karomancer/uddermayhem/BovineBaristaGame/Assets/Sprites/background@2x.png

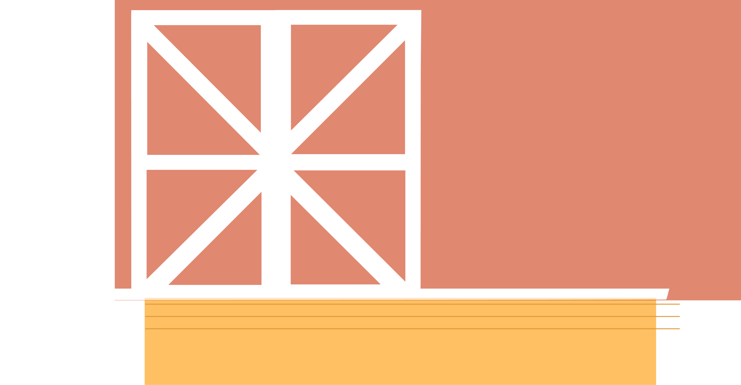
BovineBaristaGame/Assets/Sprites/background@2x.png
