karomancer/uddermayhem/BovineBaristaGame/Assets/Sprites/counter@2x.png

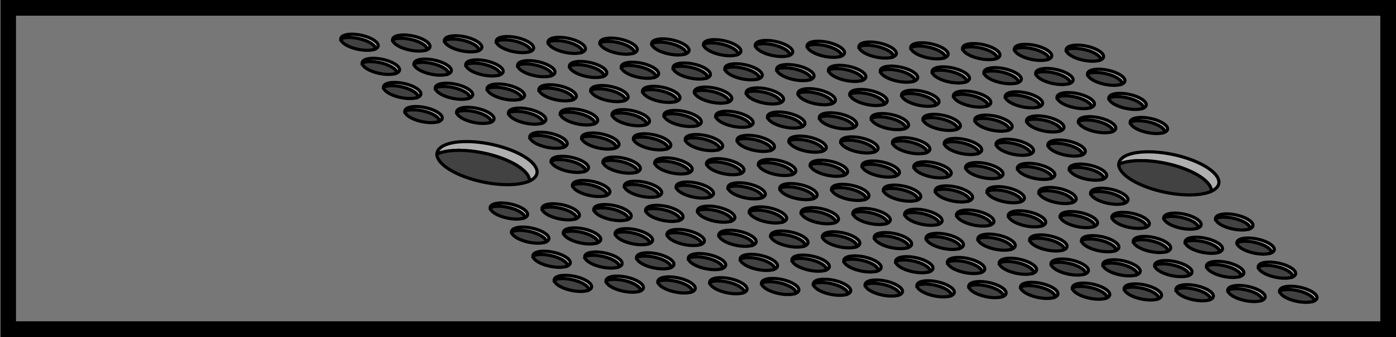
BovineBaristaGame/Assets/Sprites/counter@2x.png
