karomancer/uddermayhem/BovineBaristaGame/Assets/Sprites/cowBase@2x.png

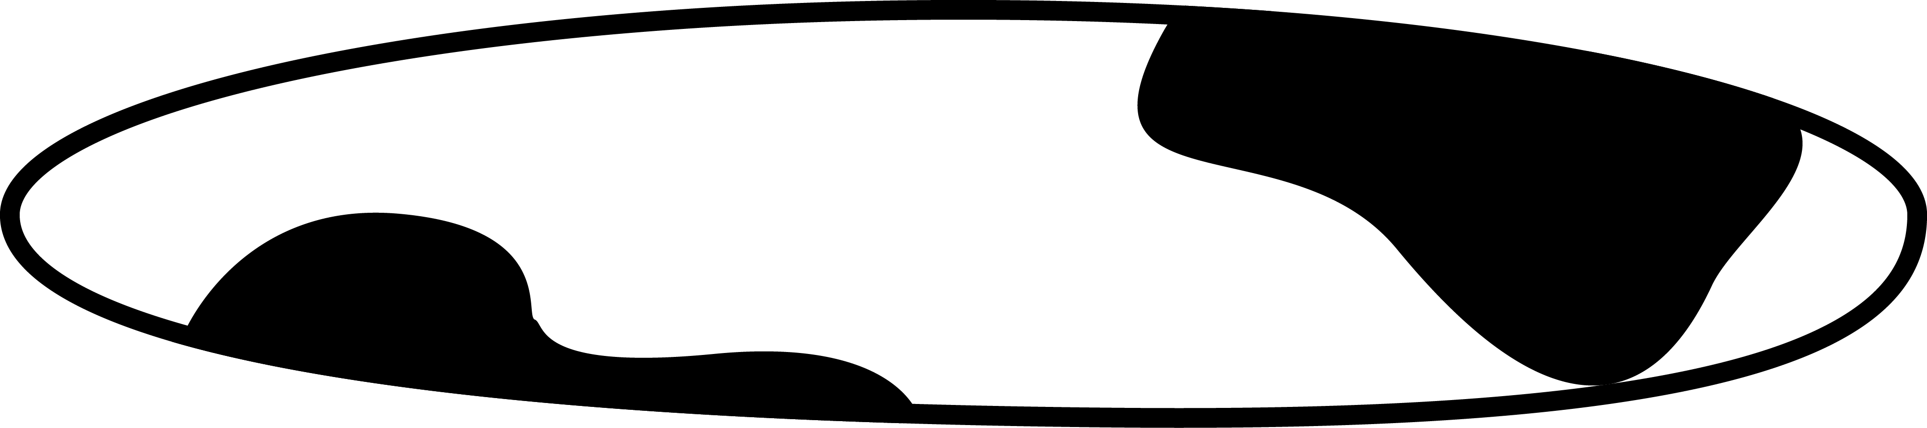
BovineBaristaGame/Assets/Sprites/cowBase@2x.png
