karomancer/uddermayhem/BovineBaristaGame/Assets/Sprites/lady_spritemap@2x-8.png

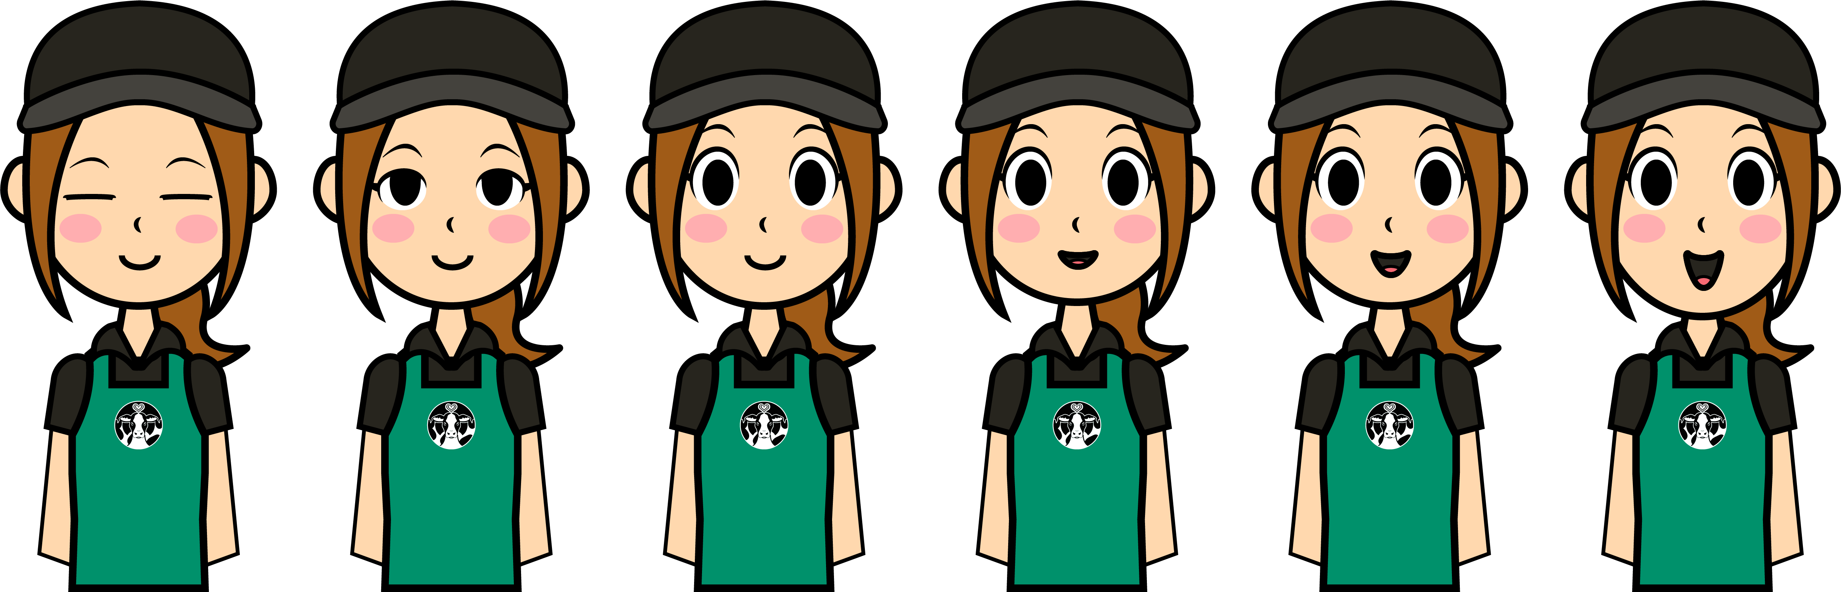
BovineBaristaGame/Assets/Sprites/lady_spritemap@2x-8.png
