karomancer/uddermayhem/BovineBaristaGame/Assets/Sprites/MoosicCoffee@2x.png

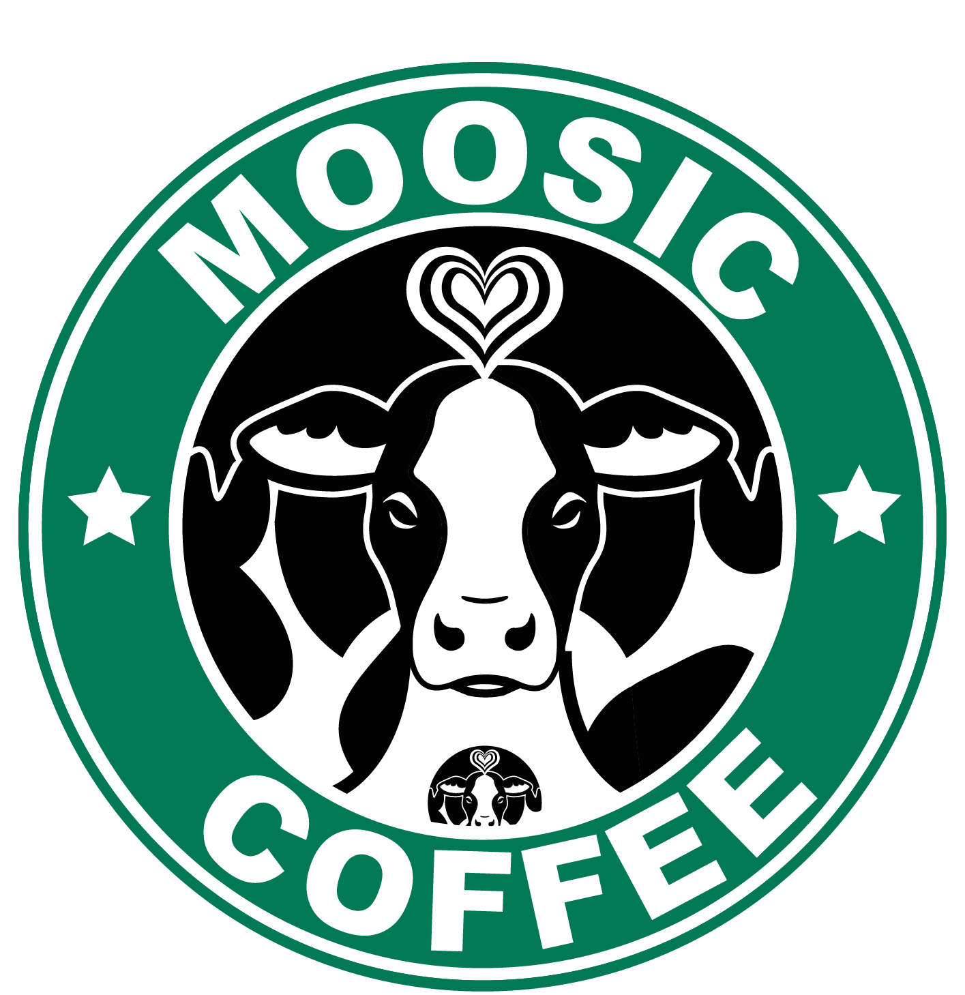
BovineBaristaGame/Assets/Sprites/MoosicCoffee@2x.png
