karomancer/uddermayhem/BovineBaristaGame/Assets/Sprites/MoosicCoffeeCup@2x.png

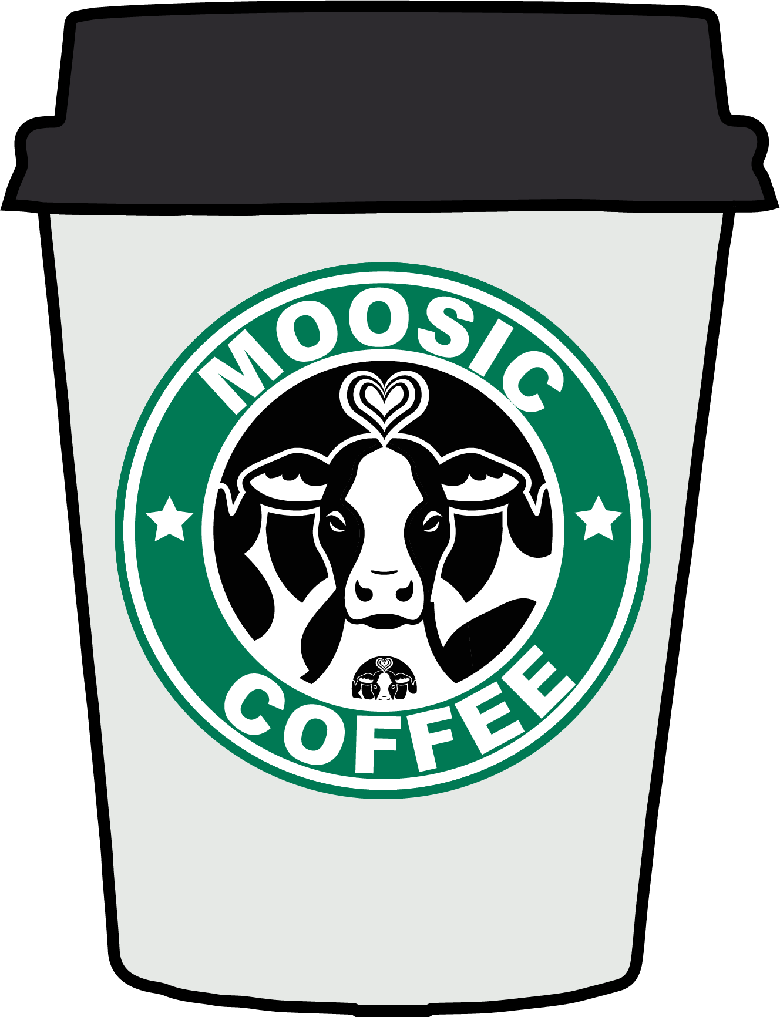
BovineBaristaGame/Assets/Sprites/MoosicCoffeeCup@2x.png
