karomancer/uddermayhem/BovineBaristaGame/Assets/Sprites/teatSpritesheet@2x 1.png

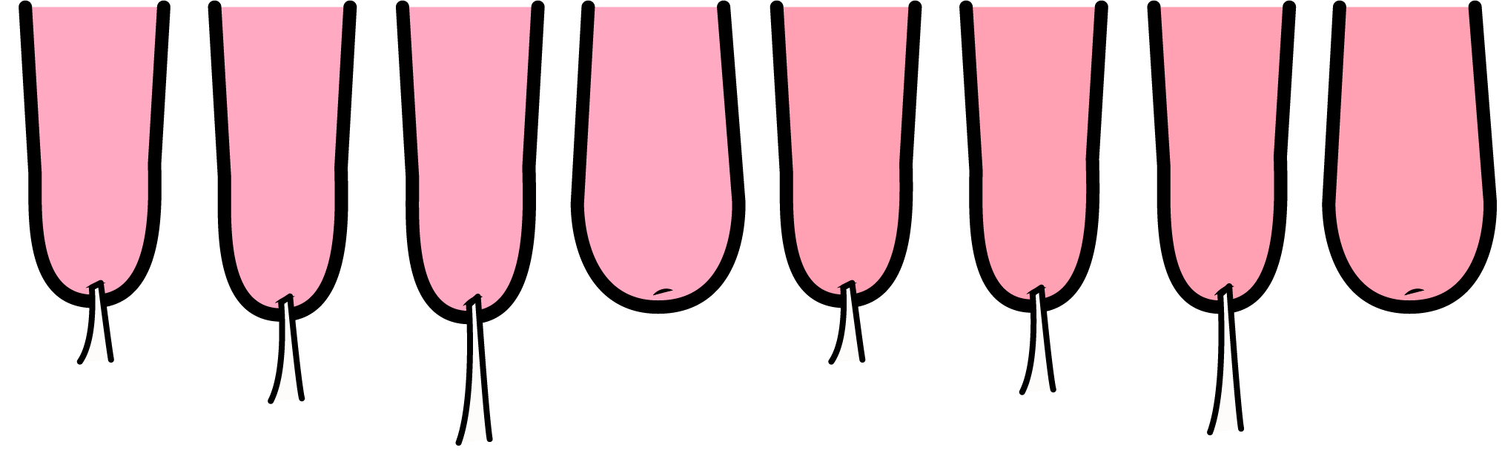
BovineBaristaGame/Assets/Sprites/teatSpritesheet@2x 1.png
