karomancer/uddermayhem/BovineBaristaGame/Assets/Sprites/TitleScreen/2x/Cloud@2x-8.png

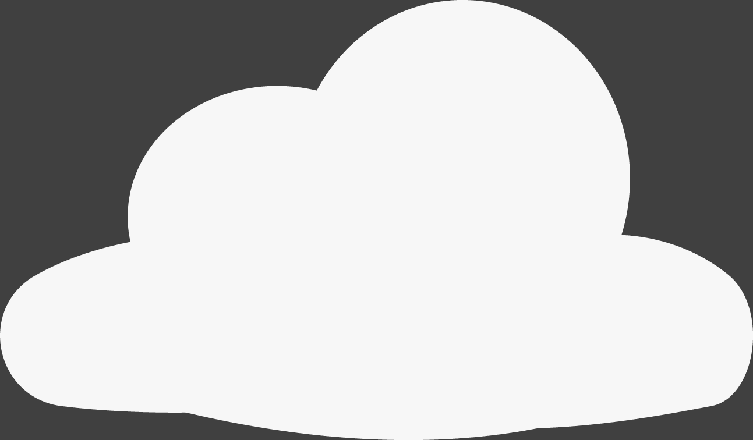
BovineBaristaGame/Assets/Sprites/TitleScreen/2x/Cloud@2x-8.png
