karomancer/uddermayhem/BovineBaristaGame/Assets/Sprites/TitleScreen/2x/MoosicCafe@2x-8.png

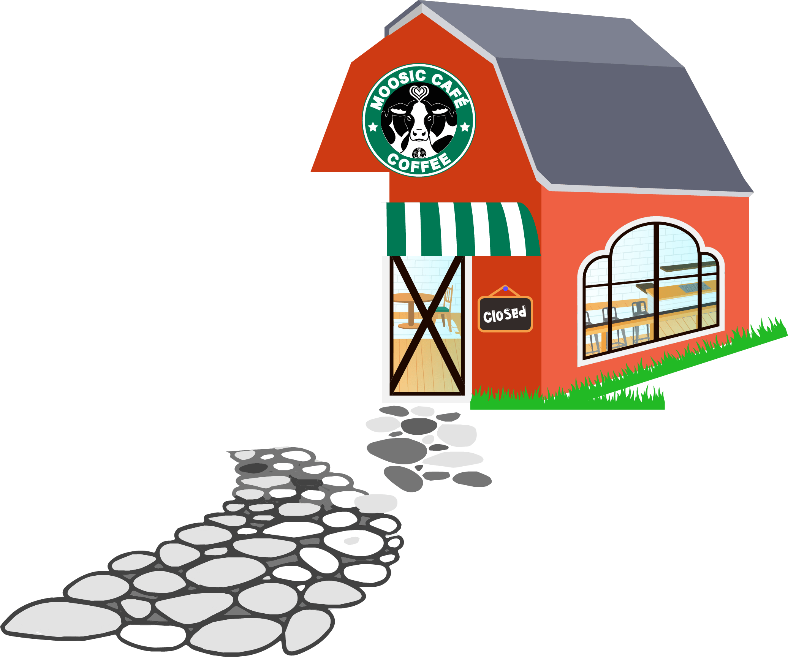
BovineBaristaGame/Assets/Sprites/TitleScreen/2x/MoosicCafe@2x-8.png
