karomancer/uddermayhem/BovineBaristaGame/Assets/Sprites/TitleScreen/2x/Sun@2x-8.png

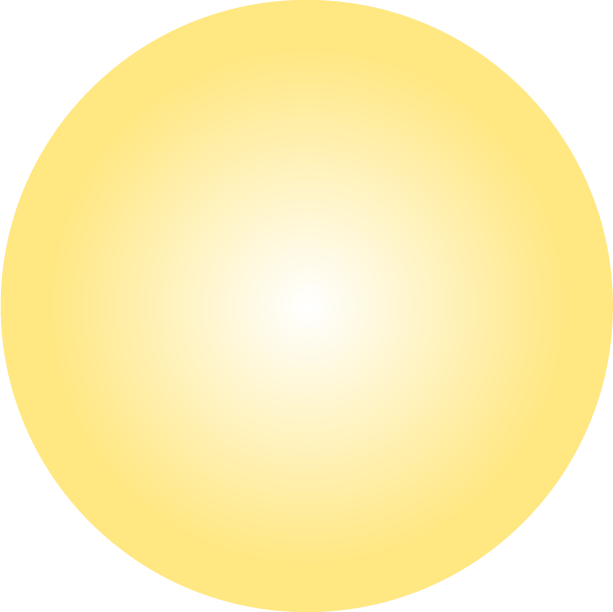
BovineBaristaGame/Assets/Sprites/TitleScreen/2x/Sun@2x-8.png
