karomancer/uddermayhem/BovineBaristaGame/Assets/squeezeMessage@2x.png

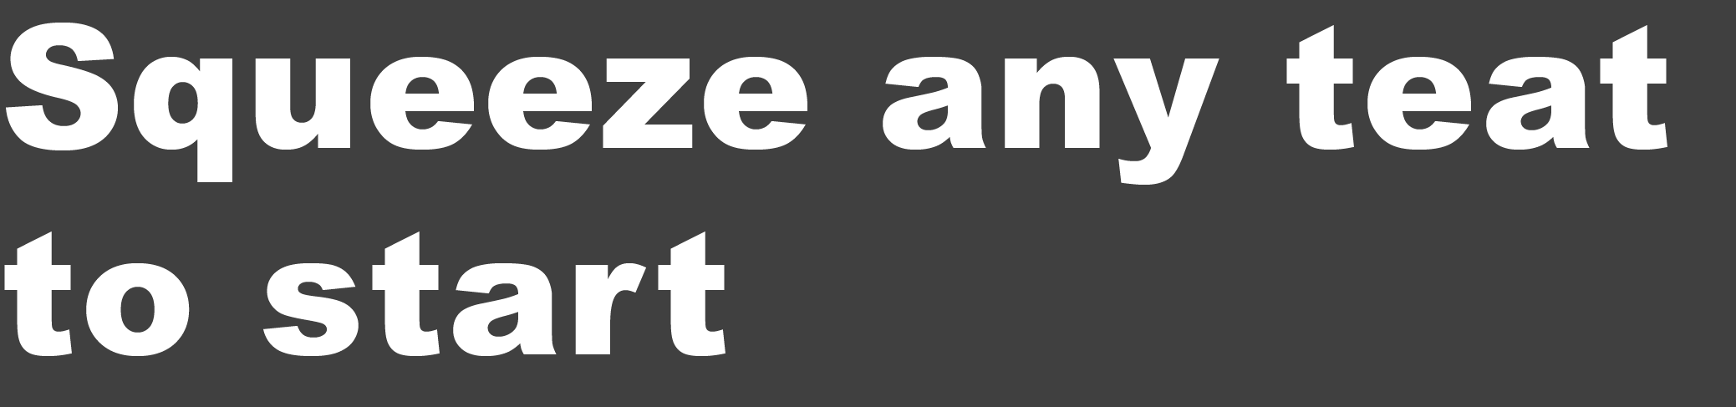
BovineBaristaGame/Assets/squeezeMessage@2x.png
