karomancer/uddermayhem/CAD/gcode/122325.png

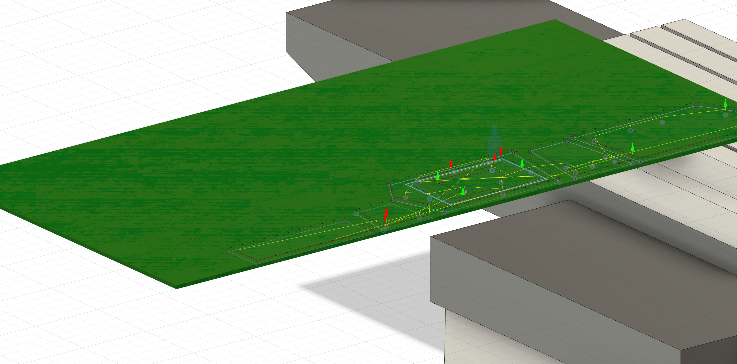
CAD/gcode/122325.png
