karomancer/uddermayhem/MakeMagazine/udder_inset.stl

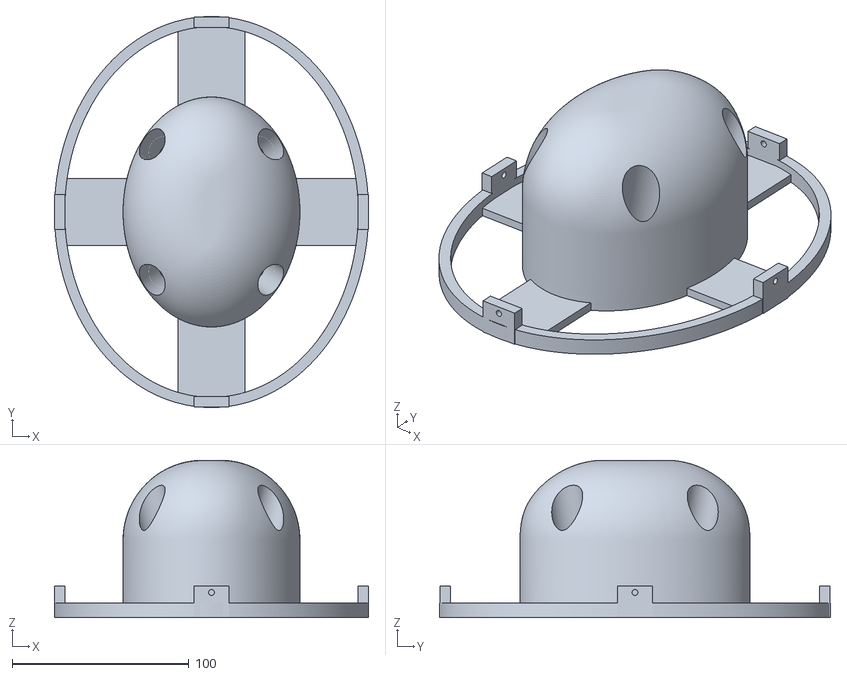
[picture p33: CAD file, 2026-09-23]
MakeMagazine/udder_inset.stl
177.6 x 221.1 x 89.0
