karomancer/uddermayhem/MakeMagazine/udder_moldbox_1pc.stl

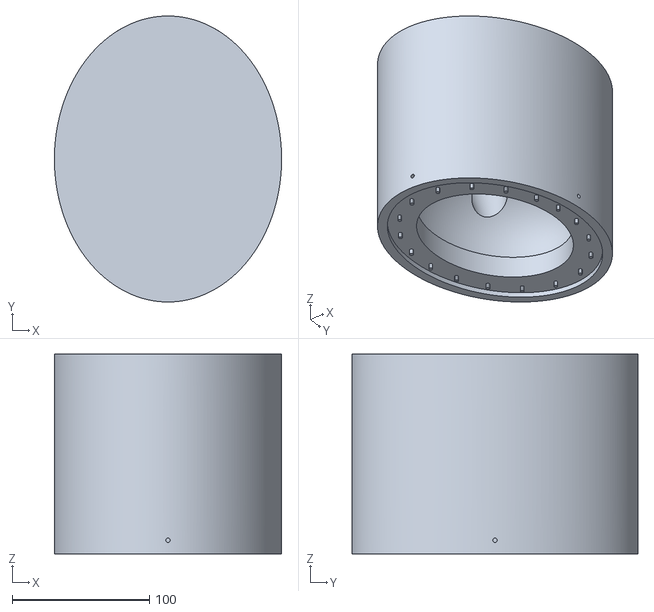
[picture p34: CAD file, 2026-09-23]
MakeMagazine/udder_moldbox_1pc.stl
165.6 x 208.5 x 145.7
