karomancer/uddermayhem/CAD/brackets/ContainerInsert.stl

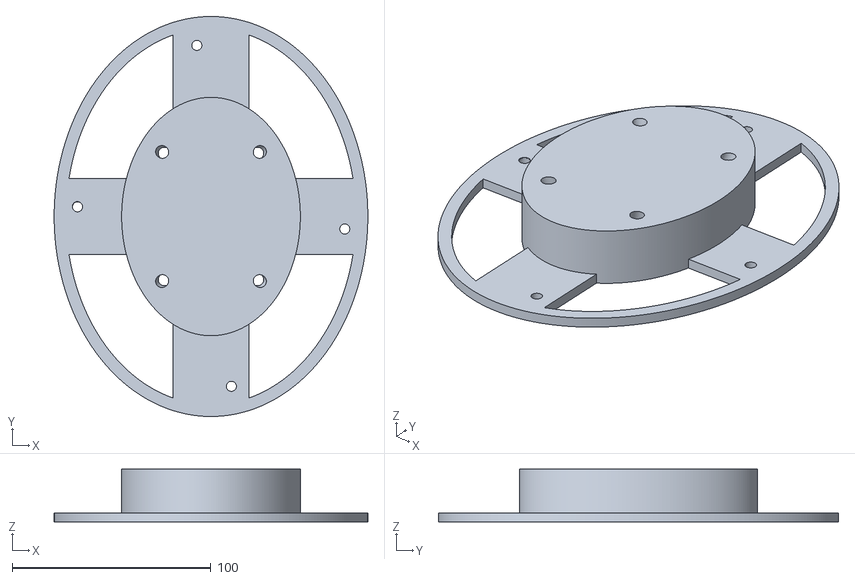
[picture p35: CAD file, 2026-01-06]
CAD/brackets/ContainerInsert.stl
158.0 x 201.4 x 26.5
