karomancer/uddermayhem/CAD/silicone_top.dxf

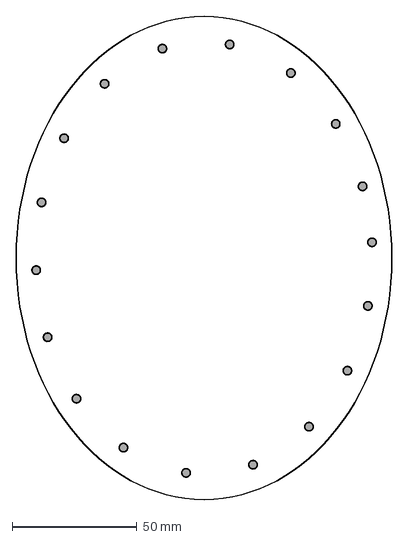
[picture p36: CAD file, 2026-01-06]
CAD/silicone_top.dxf
150.6 x 193.6 mm
