karomancer/uddermayhem/MakeMagazine/udder_topbrace.stl

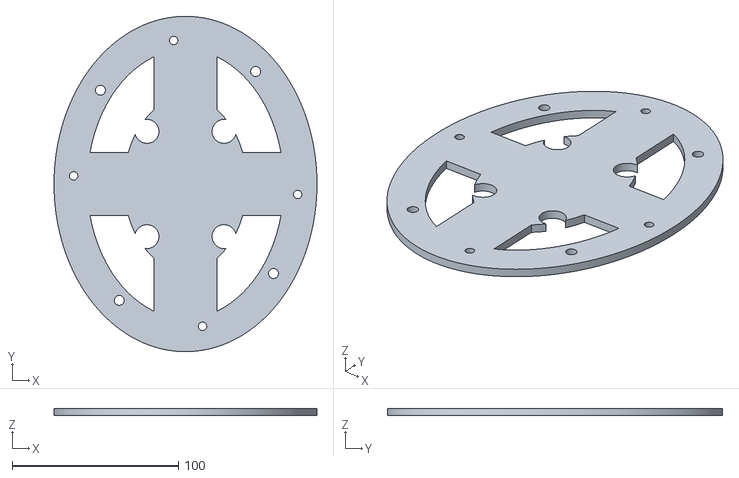
[picture p37: CAD file, 2026-09-23]
MakeMagazine/udder_topbrace.stl
158.0 x 201.4 x 4.50
