karomancer/uddermayhem/CAD/brackets/ButtShelf.stl

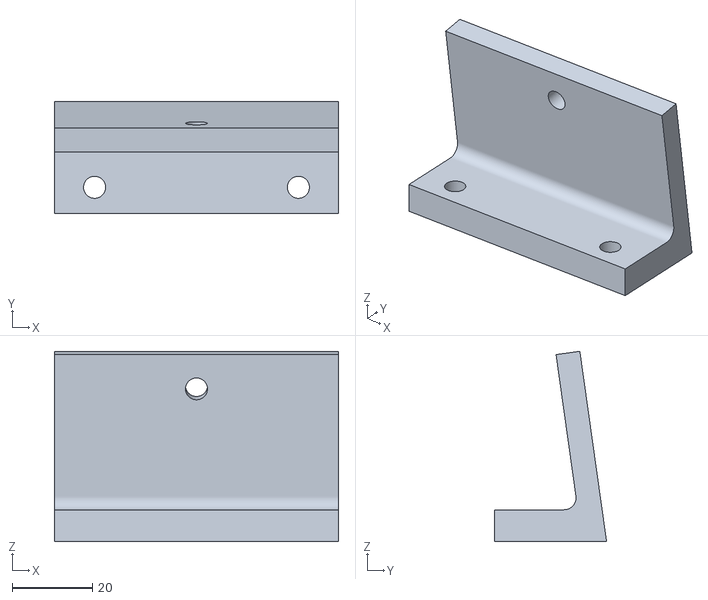
[picture p38: CAD file, 2026-01-06]
CAD/brackets/ButtShelf.stl
70.8 x 28.0 x 47.5
