karomancer/uddermayhem/CAD/brackets/BellyShelf.stl

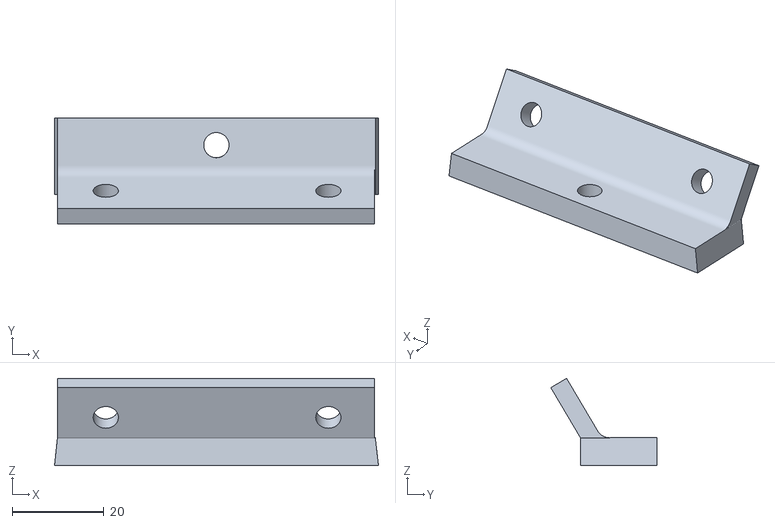
[picture p39: CAD file, 2026-01-06]
CAD/brackets/BellyShelf.stl
70.6 x 23.2 x 19.0
