karomancer/uddermayhem/CAD/brackets/RightButtBracket.stl

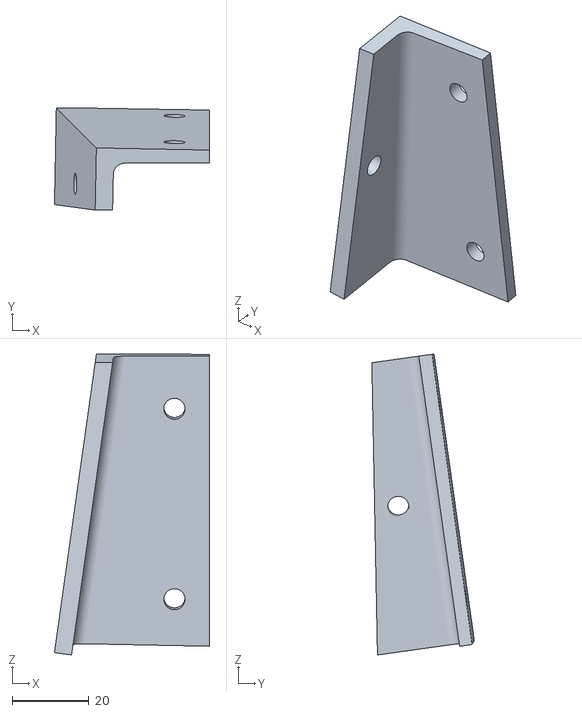
[picture p40: CAD file, 2026-01-06]
CAD/brackets/RightButtBracket.stl
40.4 x 26.6 x 78.3
