karomancer/uddermayhem/CAD/top_spacer.stl

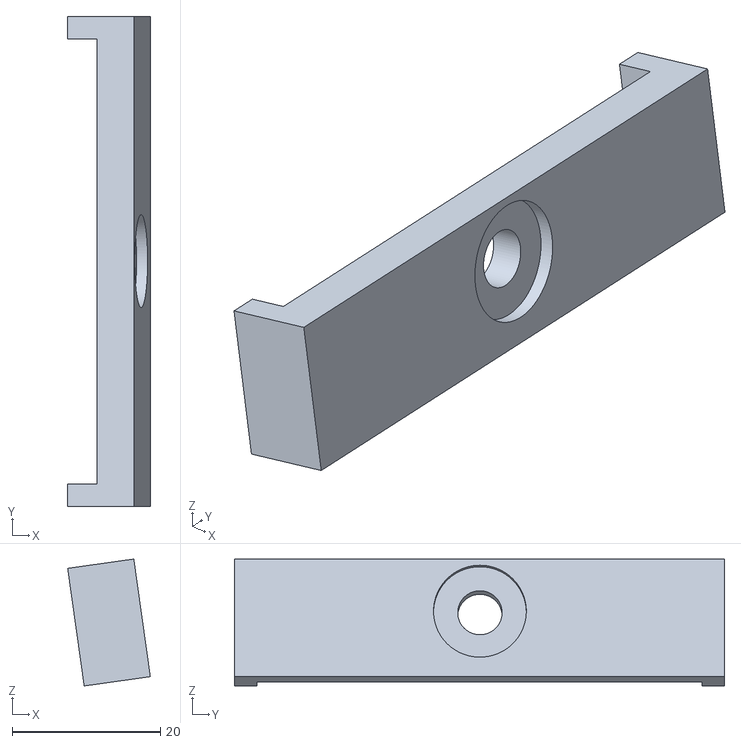
[picture p41: CAD file, 2026-01-06]
CAD/top_spacer.stl
11.1 x 66.0 x 17.1
