karomancer/uddermayhem/CAD/InnerUdder.stl

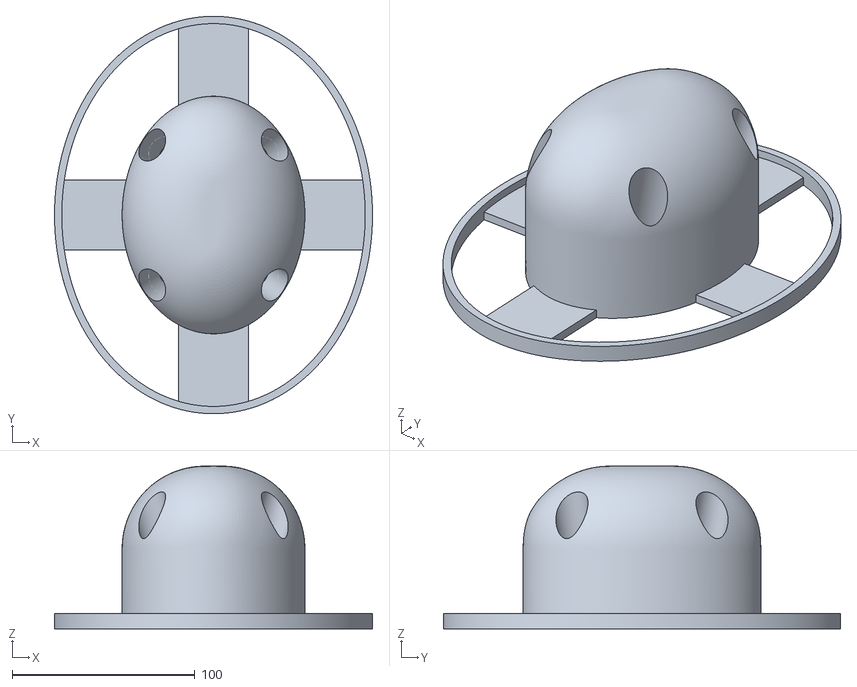
[picture p42: CAD file, 2026-01-06]
CAD/InnerUdder.stl
174.0 x 217.4 x 89.0
