karomancer/uddermayhem/CAD/Brace2.stl

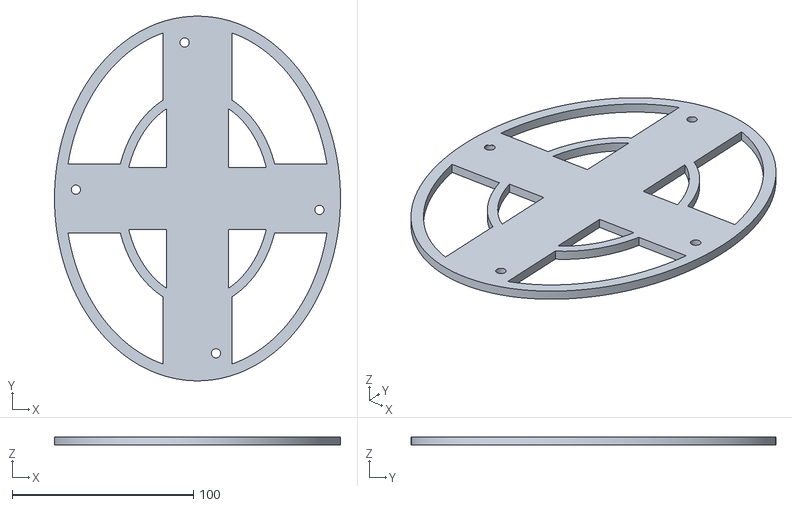
[picture p43: CAD file, 2026-01-06]
CAD/Brace2.stl
158.0 x 201.4 x 4.50
