karomancer/uddermayhem/CAD/Brace1.stl

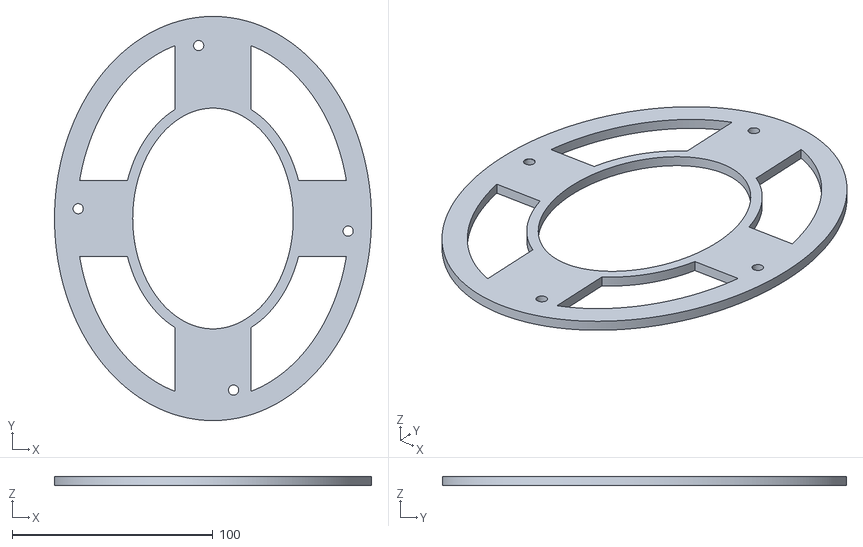
[picture p44: CAD file, 2026-01-06]
CAD/Brace1.stl
158.0 x 201.4 x 4.50
