karomancer/uddermayhem/CAD/Brace.stl

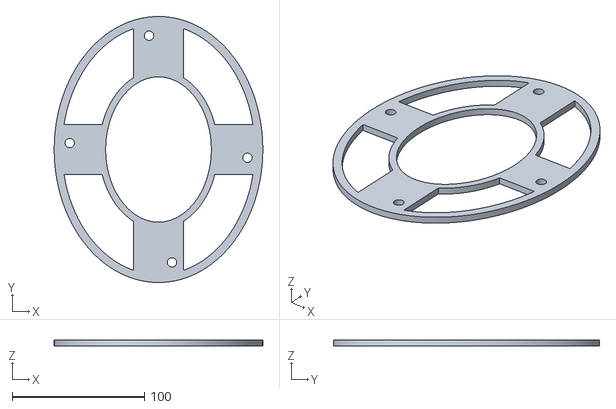
[picture p45: CAD file, 2026-01-06]
CAD/Brace.stl
158.0 x 201.4 x 4.50
