karomancer/uddermayhem/CAD/NewBrace2Holes.stl

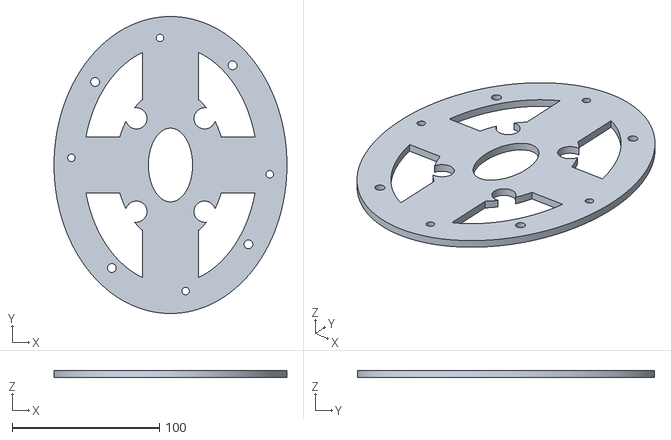
[picture p46: CAD file, 2026-01-06]
CAD/NewBrace2Holes.stl
158.0 x 201.4 x 4.50
