karomancer/uddermayhem/CAD/ScreenShelfBackBracket.stl

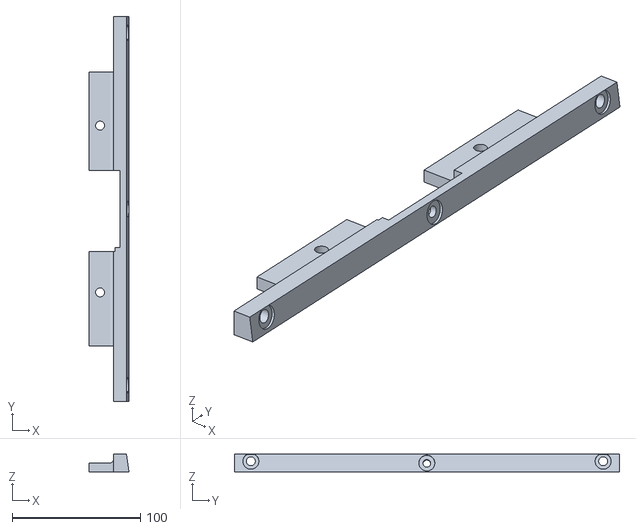
[picture p47: CAD file, 2026-01-06]
CAD/ScreenShelfBackBracket.stl
31.2 x 300.8 x 13.8
